jrozner/the-intercept-2019/firmware/main/cmd_wifi.c

#include <stdio.h>
#include <string.h>
#include "esp_log.h"
#include "esp_console.h"
#include "argtable3/argtable3.h"
#include "freertos/FreeRTOS.h"
#include "freertos/event_groups.h"
#include "esp_wifi.h"
#include "tcpip_adapter.h"
#include "esp_event_loop.h"

static EventGroupHandle_t wifi_event_group;
const int CONNECTED_BIT = BIT0;

static esp_err_t event_handler(void *ctx, system_event_t *event) {
    switch(event->event_id) {
    case SYSTEM_EVENT_STA_GOT_IP:
        xEventGroupSetBits(wifi_event_group, CONNECTED_BIT);
        break;
    case SYSTEM_EVENT_STA_DISCONNECTED:
        esp_wifi_connect();
        xEventGroupClearBits(wifi_event_group, CONNECTED_BIT);
        break;
    default:
        break;
    }
    return ESP_OK;
}

static void initialise_wifi(void)
{
    esp_log_level_set("wifi", ESP_LOG_WARN);
    static bool initialized = false;
    if (initialized) {
        return;
    }
    tcpip_adapter_init();
    wifi_event_group = xEventGroupCreate();
    ESP_ERROR_CHECK( esp_event_loop_init(event_handler, NULL) );
    wifi_init_config_t cfg = WIFI_INIT_CONFIG_DEFAULT();
    ESP_ERROR_CHECK( esp_wifi_init(&cfg) );
    ESP_ERROR_CHECK( esp_wifi_set_storage(WIFI_STORAGE_RAM) );
    ESP_ERROR_CHECK( esp_wifi_set_mode(WIFI_MODE_NULL) );
    ESP_ERROR_CHECK( esp_wifi_start() );
    initialized = true;
}

static bool wifi_join(const char* ssid, const char* pass, int timeout_ms) {
    initialise_wifi();
    wifi_config_t wifi_config = { 0 };
    strncpy((char*) wifi_config.sta.ssid, ssid, sizeof(wifi_config.sta.ssid));
    if (pass) {
        strncpy((char*) wifi_config.sta.password, pass, sizeof(wifi_config.sta.password));
    }

    ESP_ERROR_CHECK(esp_wifi_set_mode(WIFI_MODE_STA));
    ESP_ERROR_CHECK(esp_wifi_set_config(ESP_IF_WIFI_STA, &wifi_config));
    ESP_ERROR_CHECK(esp_wifi_connect());

    int bits = xEventGroupWaitBits(wifi_event_group, CONNECTED_BIT,
            1, 1, timeout_ms / portTICK_PERIOD_MS);
    return (bits & CONNECTED_BIT) != 0;
}
